antfriend/Anubis/Daughterboard/fabrication/jlcpcb_2026-07-11_r15/reports/Daughterboard_erc_report.txt

ERC report (2026-07-11T15:29:56, Encoding UTF8)
Report includes: Errors, Warnings

***** Sheet /
[footprint_link_issues]: The current configuration does not include the footprint library 'Connector_USB'
    ; warning
    @(36.83 mm, 50.80 mm): Symbol J1 [USB_C_SINK_GCT_6PAD]
[footprint_link_issues]: The current configuration does not include the footprint library 'Resistor_SMD'
    ; warning
    @(36.83 mm, 83.82 mm): Symbol R1 [TWO_PIN]
[footprint_link_issues]: The current configuration does not include the footprint library 'Resistor_SMD'
    ; warning
    @(36.83 mm, 97.79 mm): Symbol R2 [TWO_PIN]
[footprint_link_issues]: The current configuration does not include the footprint library 'Fuse'
    ; warning
    @(85.09 mm, 50.80 mm): Symbol F1 [TWO_PIN]
[footprint_link_issues]: The current configuration does not include the footprint library 'Diode_SMD'
    ; warning
    @(85.09 mm, 67.31 mm): Symbol D1 [TWO_PIN]
[footprint_link_issues]: The current configuration does not include the footprint library 'Capacitor_SMD'
    ; warning
    @(85.09 mm, 83.82 mm): Symbol C1 [TWO_PIN]
[footprint_link_issues]: The current configuration does not include the footprint library 'Capacitor_SMD'
    ; warning
    @(85.09 mm, 97.79 mm): Symbol C2 [TWO_PIN]
[footprint_link_issues]: The current configuration does not include the footprint library 'Package_TO_SOT_SMD'
    ; warning
    @(91.44 mm, 264.16 mm): Symbol U3 [AP63200WU]
[footprint_link_issues]: The current configuration does not include the footprint library 'Package_TO_SOT_SMD'
    ; warning
    @(91.44 mm, 341.63 mm): Symbol U4 [AP63200WU]
[footprint_link_issues]: The current configuration does not include the footprint library 'Fuse'
    ; warning
    @(97.79 mm, 149.86 mm): Symbol F2 [TWO_PIN]
[footprint_link_issues]: The current configuration does not include the footprint library 'Fuse'
    ; warning
    @(97.79 mm, 180.34 mm): Symbol F3 [TWO_PIN]
[footprint_link_issues]: The current configuration does not include the footprint library 'Connector_JST'
    ; warning
    @(149.86 mm, 163.83 mm): Symbol J7 [CONN_3]
[footprint_link_issues]: The current configuration does not include the footprint library 'Inductor_SMD'
    ; warning
    @(149.86 mm, 246.38 mm): Symbol L1 [TWO_PIN]
[footprint_link_issues]: The current configuration does not include the footprint library 'Capacitor_SMD'
    ; warning
    @(149.86 mm, 260.35 mm): Symbol C11 [TWO_PIN]
[footprint_link_issues]: The current configuration does not include the footprint library 'Capacitor_SMD'
    ; warning
    @(149.86 mm, 274.32 mm): Symbol C12 [TWO_PIN]
[footprint_link_issues]: The current configuration does not include the footprint library 'Resistor_SMD'
    ; warning
    @(149.86 mm, 289.56 mm): Symbol R10 [TWO_PIN]
[footprint_link_issues]: The current configuration does not include the footprint library 'Inductor_SMD'
    ; warning
    @(149.86 mm, 323.85 mm): Symbol L2 [TWO_PIN]
[footprint_link_issues]: The current configuration does not include the footprint library 'Capacitor_SMD'
    ; warning
    @(149.86 mm, 337.82 mm): Symbol C16 [TWO_PIN]
[footprint_link_issues]: The current configuration does not include the footprint library 'Capacitor_SMD'
    ; warning
    @(149.86 mm, 353.06 mm): Symbol C21 [TWO_PIN]
[footprint_link_issues]: The current configuration does not include the footprint library 'Resistor_SMD'
    ; warning
    @(149.86 mm, 367.03 mm): Symbol R13 [TWO_PIN]
[footprint_link_issues]: The current configuration does not include the footprint library 'Package_DFN_QFN'
    ; warning
    @(158.75 mm, 72.39 mm): Symbol U1 [BQ25887RGE]
[footprint_link_issues]: The current configuration does not include the footprint library 'Capacitor_SMD'
    ; warning
    @(201.93 mm, 246.38 mm): Symbol C13 [TWO_PIN]
[footprint_link_issues]: The current configuration does not include the footprint library 'Capacitor_SMD'
    ; warning
    @(201.93 mm, 260.35 mm): Symbol C14 [TWO_PIN]
[footprint_link_issues]: The current configuration does not include the footprint library 'Capacitor_SMD'
    ; warning
    @(201.93 mm, 274.32 mm): Symbol C15 [TWO_PIN]
[footprint_link_issues]: The current configuration does not include the footprint library 'Resistor_SMD'
    ; warning
    @(201.93 mm, 289.56 mm): Symbol R8 [TWO_PIN]
[footprint_link_issues]: The current configuration does not include the footprint library 'Resistor_SMD'
    ; warning
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

 ** ERC messages: 157  Errors 0  Warnings 157

 ** Ignored checks:
    - Global label only appears once in the schematic
    - Four connection points are joined together
    - SPICE model issue
    - Assigned footprint doesn't match footprint filters
