antfriend/Anubis/Daughterboard/fetoptions.bmp

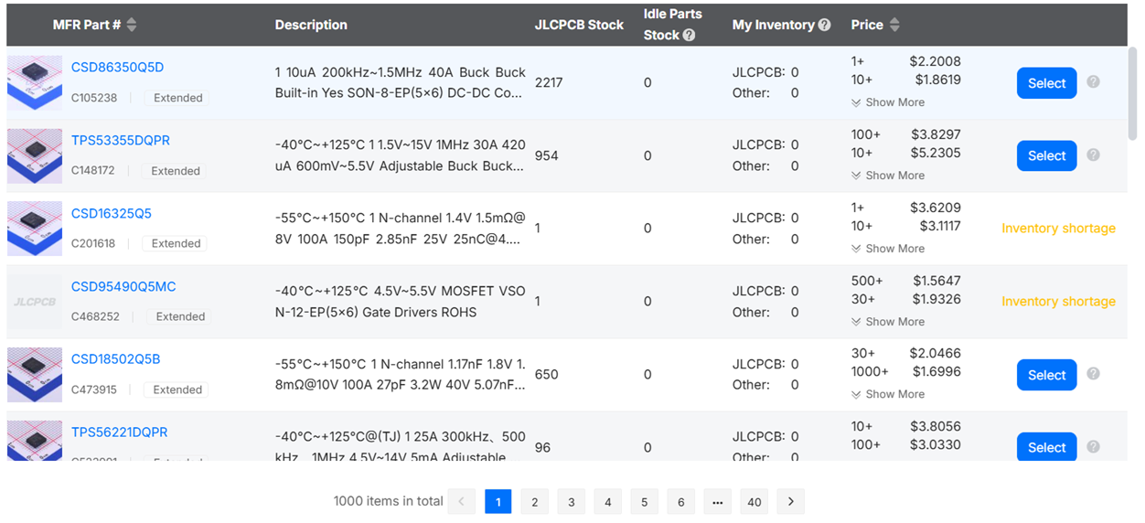
Daughterboard/fetoptions.bmp
