antfriend/Anubis/Daughterboard/tmp_csd18502_page8_vectors.png

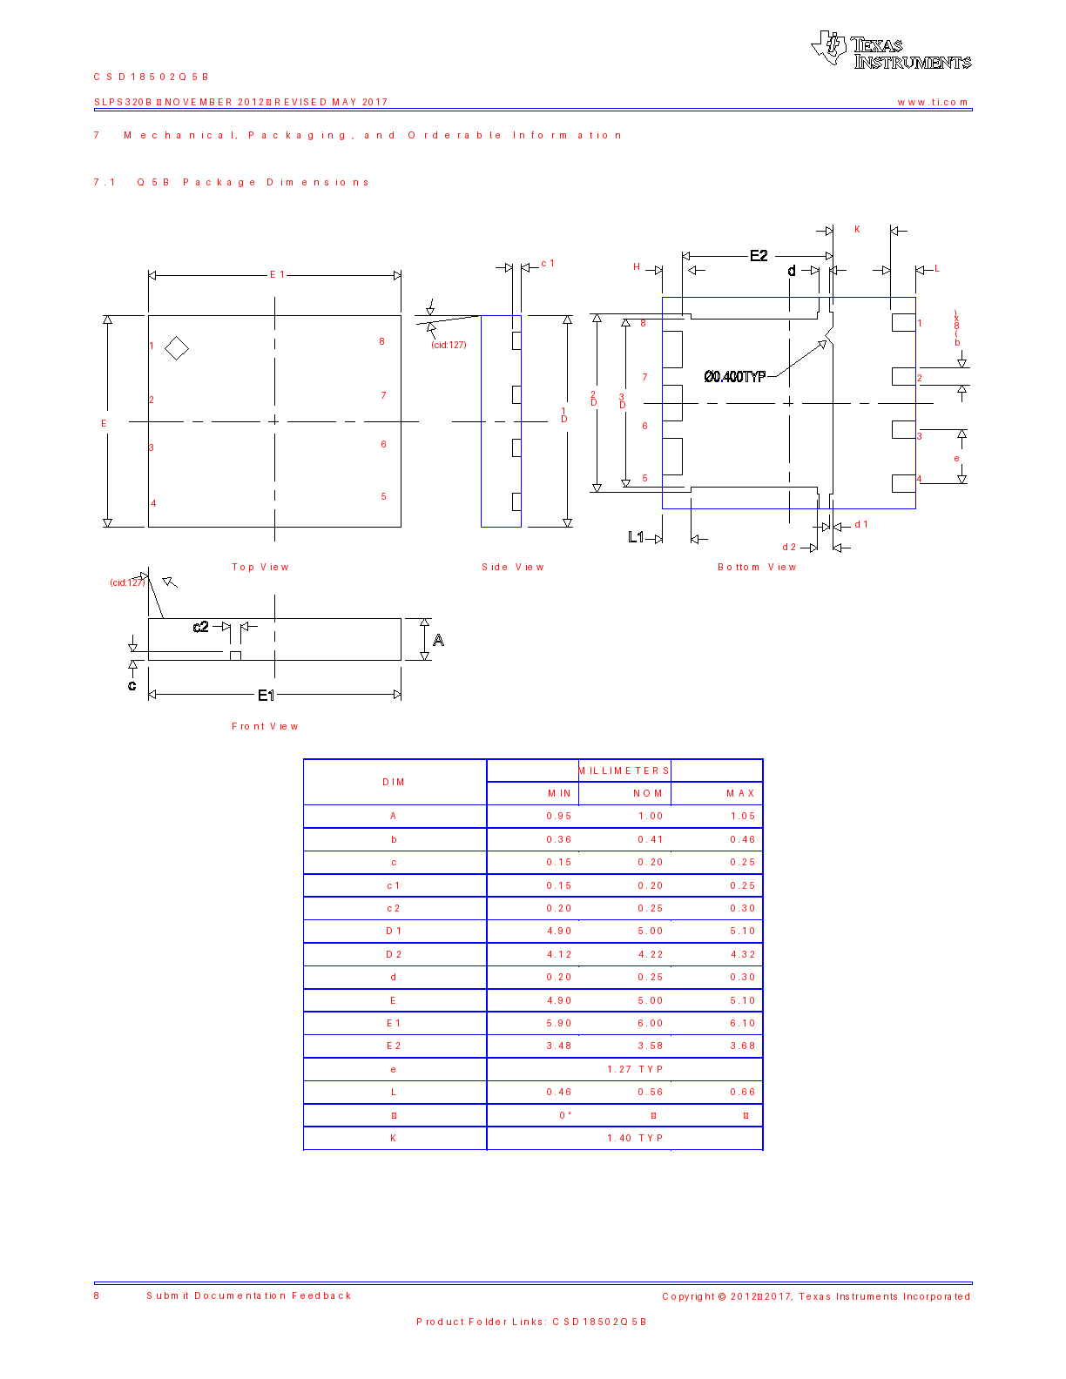
Daughterboard/tmp_csd18502_page8_vectors.png
