antfriend/Anubis/Daughterboard/tmp_csd18502_page9_vectors.png

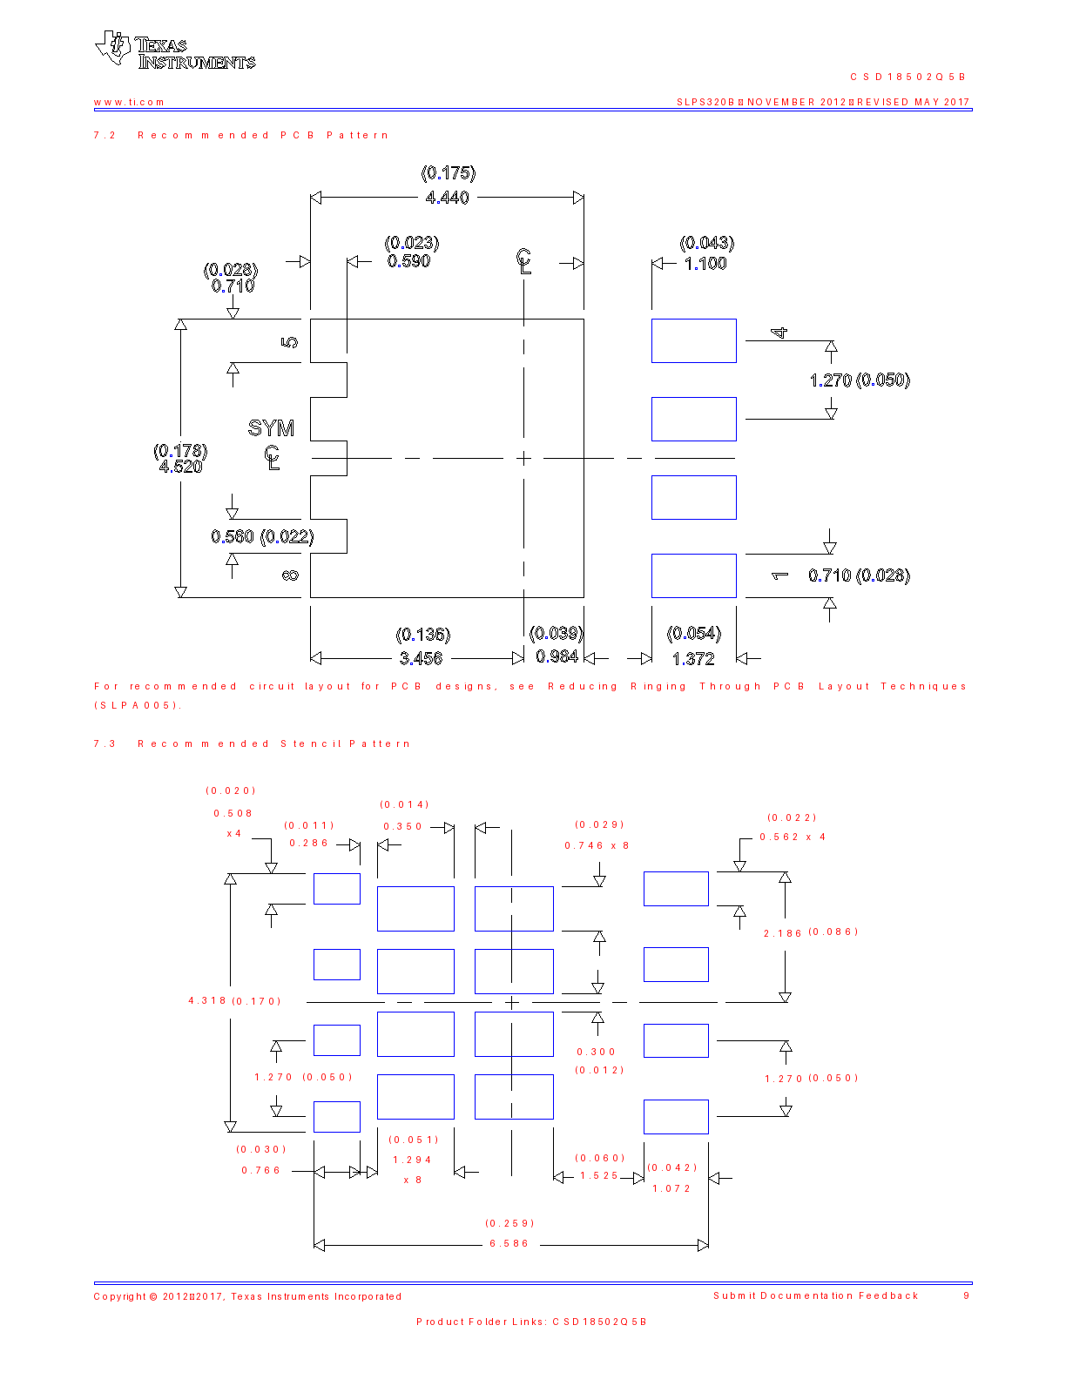
Daughterboard/tmp_csd18502_page9_vectors.png
