antfriend/Anubis/Daughterboard/x5Bottom.webp

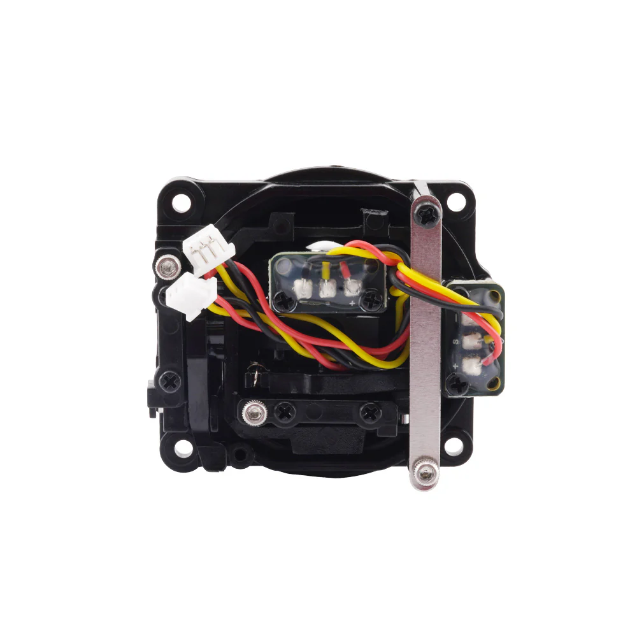
Daughterboard/x5Bottom.webp
