antfriend/Anubis/Daughterboard/x5Front.webp

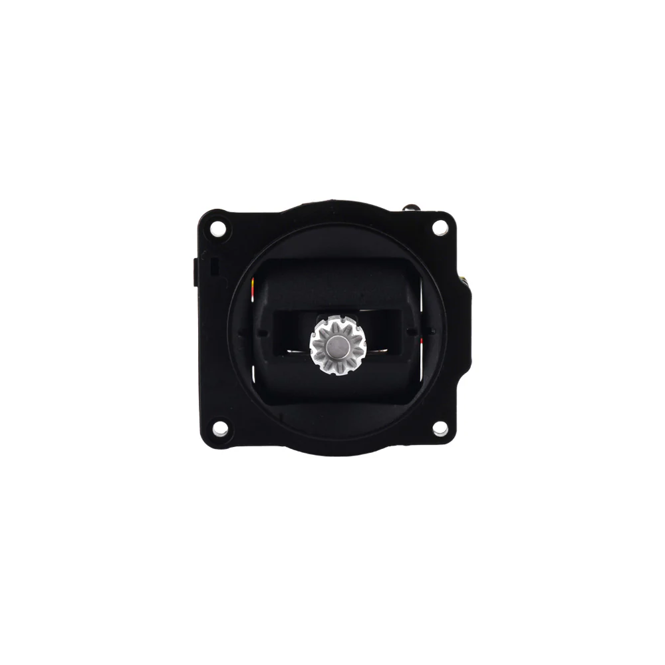
Daughterboard/x5Front.webp
