antfriend/Anubis/Hosyond_apr24b/Daughterboard/Daughterboard_pcb_bcu_ground_zone_preview.png

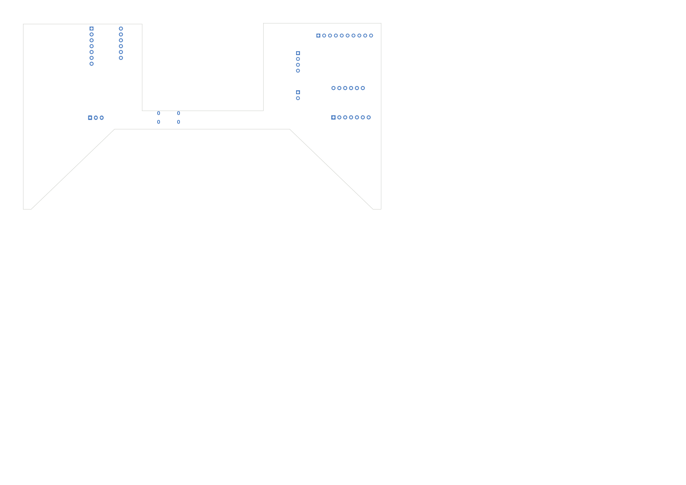
Hosyond_apr24b/Daughterboard/Daughterboard_pcb_bcu_ground_zone_preview.png
