antfriend/Anubis/Hosyond_apr24b/Daughterboard/Daughterboard_pcb_j30_5v_pad_preview.png

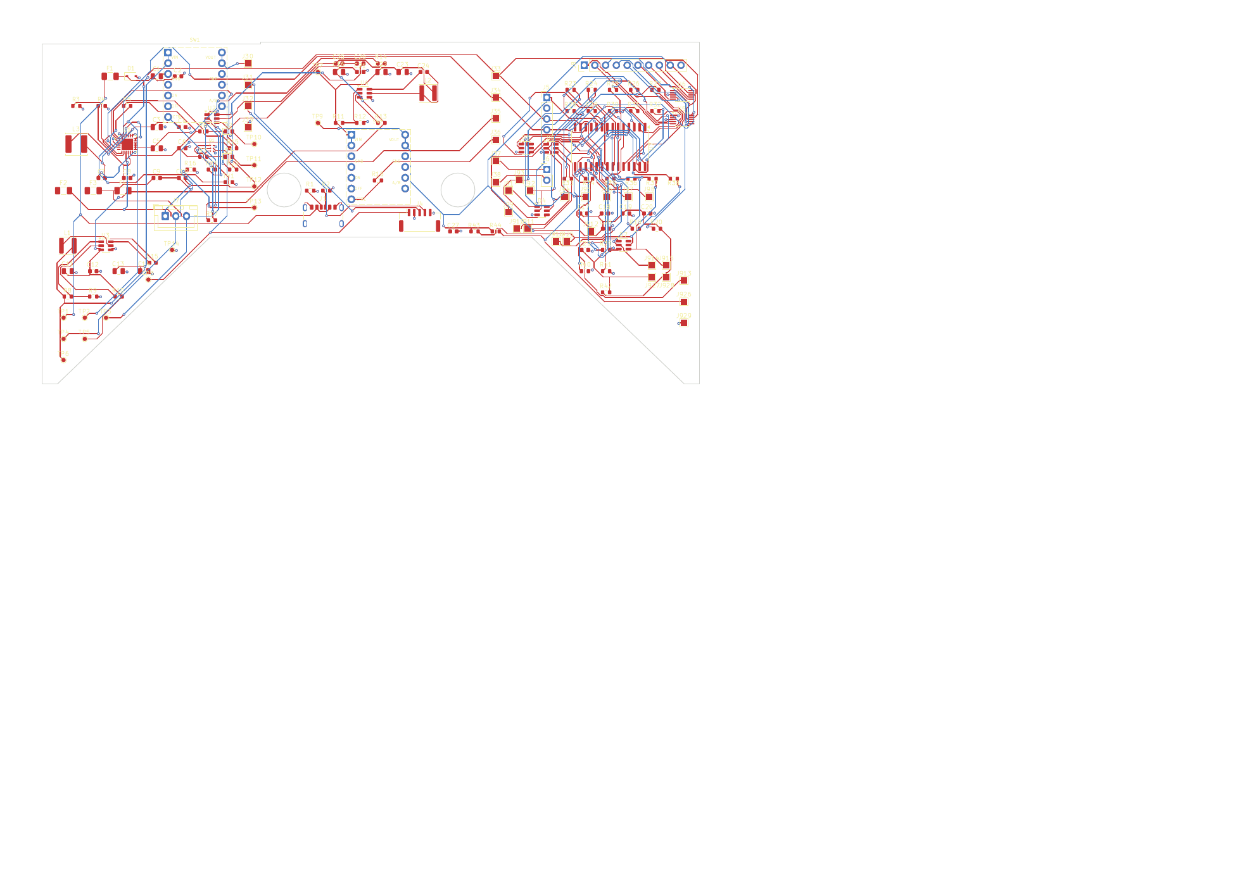
Hosyond_apr24b/Daughterboard/Daughterboard_pcb_j30_5v_pad_preview.png
