antfriend/Anubis/Hosyond_apr24b/Daughterboard/Daughterboard_pcb_power_widened_preview.png

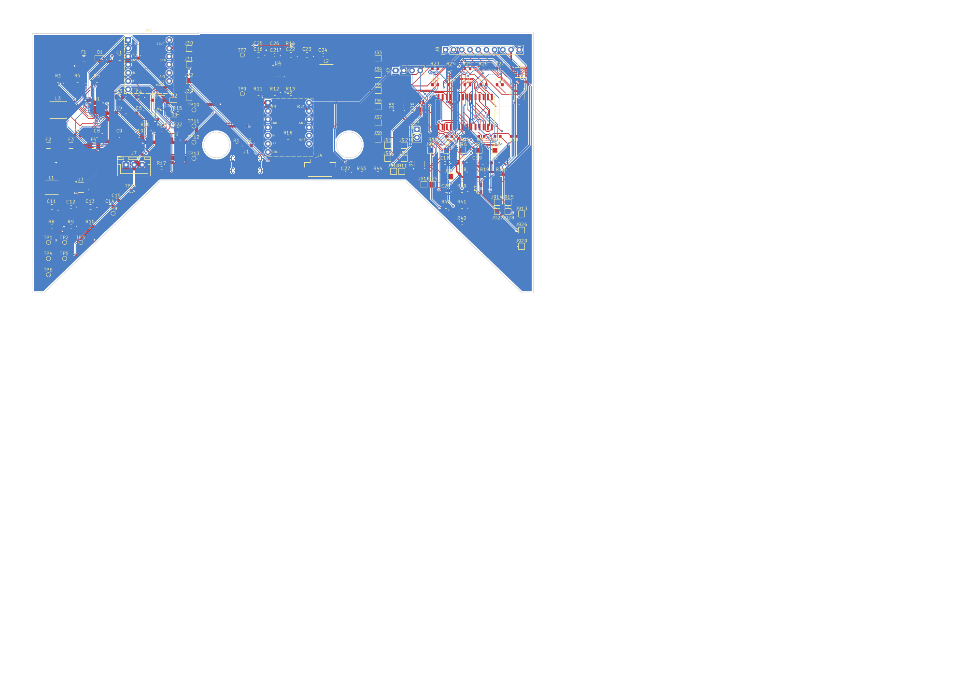
Hosyond_apr24b/Daughterboard/Daughterboard_pcb_power_widened_preview.png
