antfriend/Anubis/Hosyond_apr24b/Daughterboard/Daughterboard_pinlevel_preview-1.png

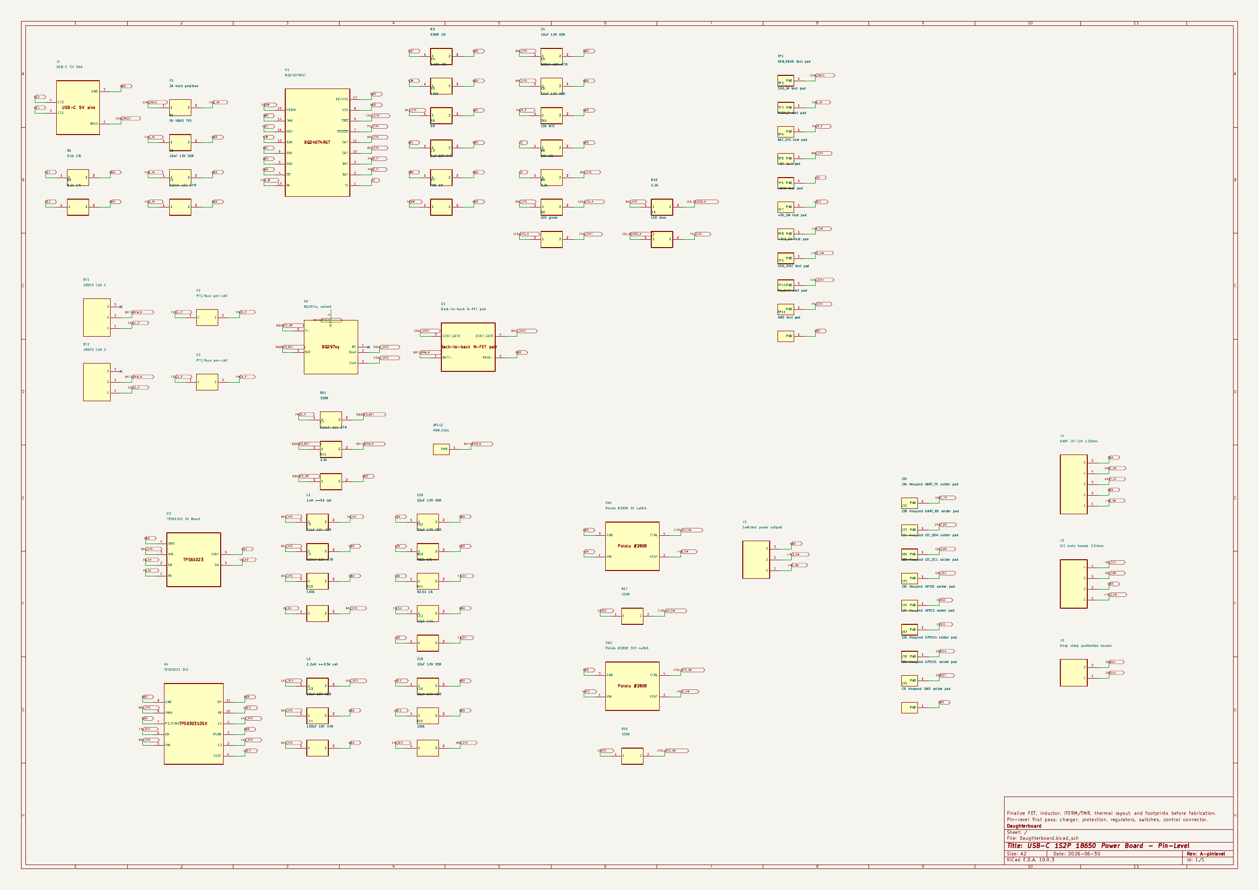
Hosyond_apr24b/Daughterboard/Daughterboard_pinlevel_preview-1.png
