antfriend/Anubis/Hosyond_apr24b/Daughterboard/Daughterboard_pinlevel.pdf

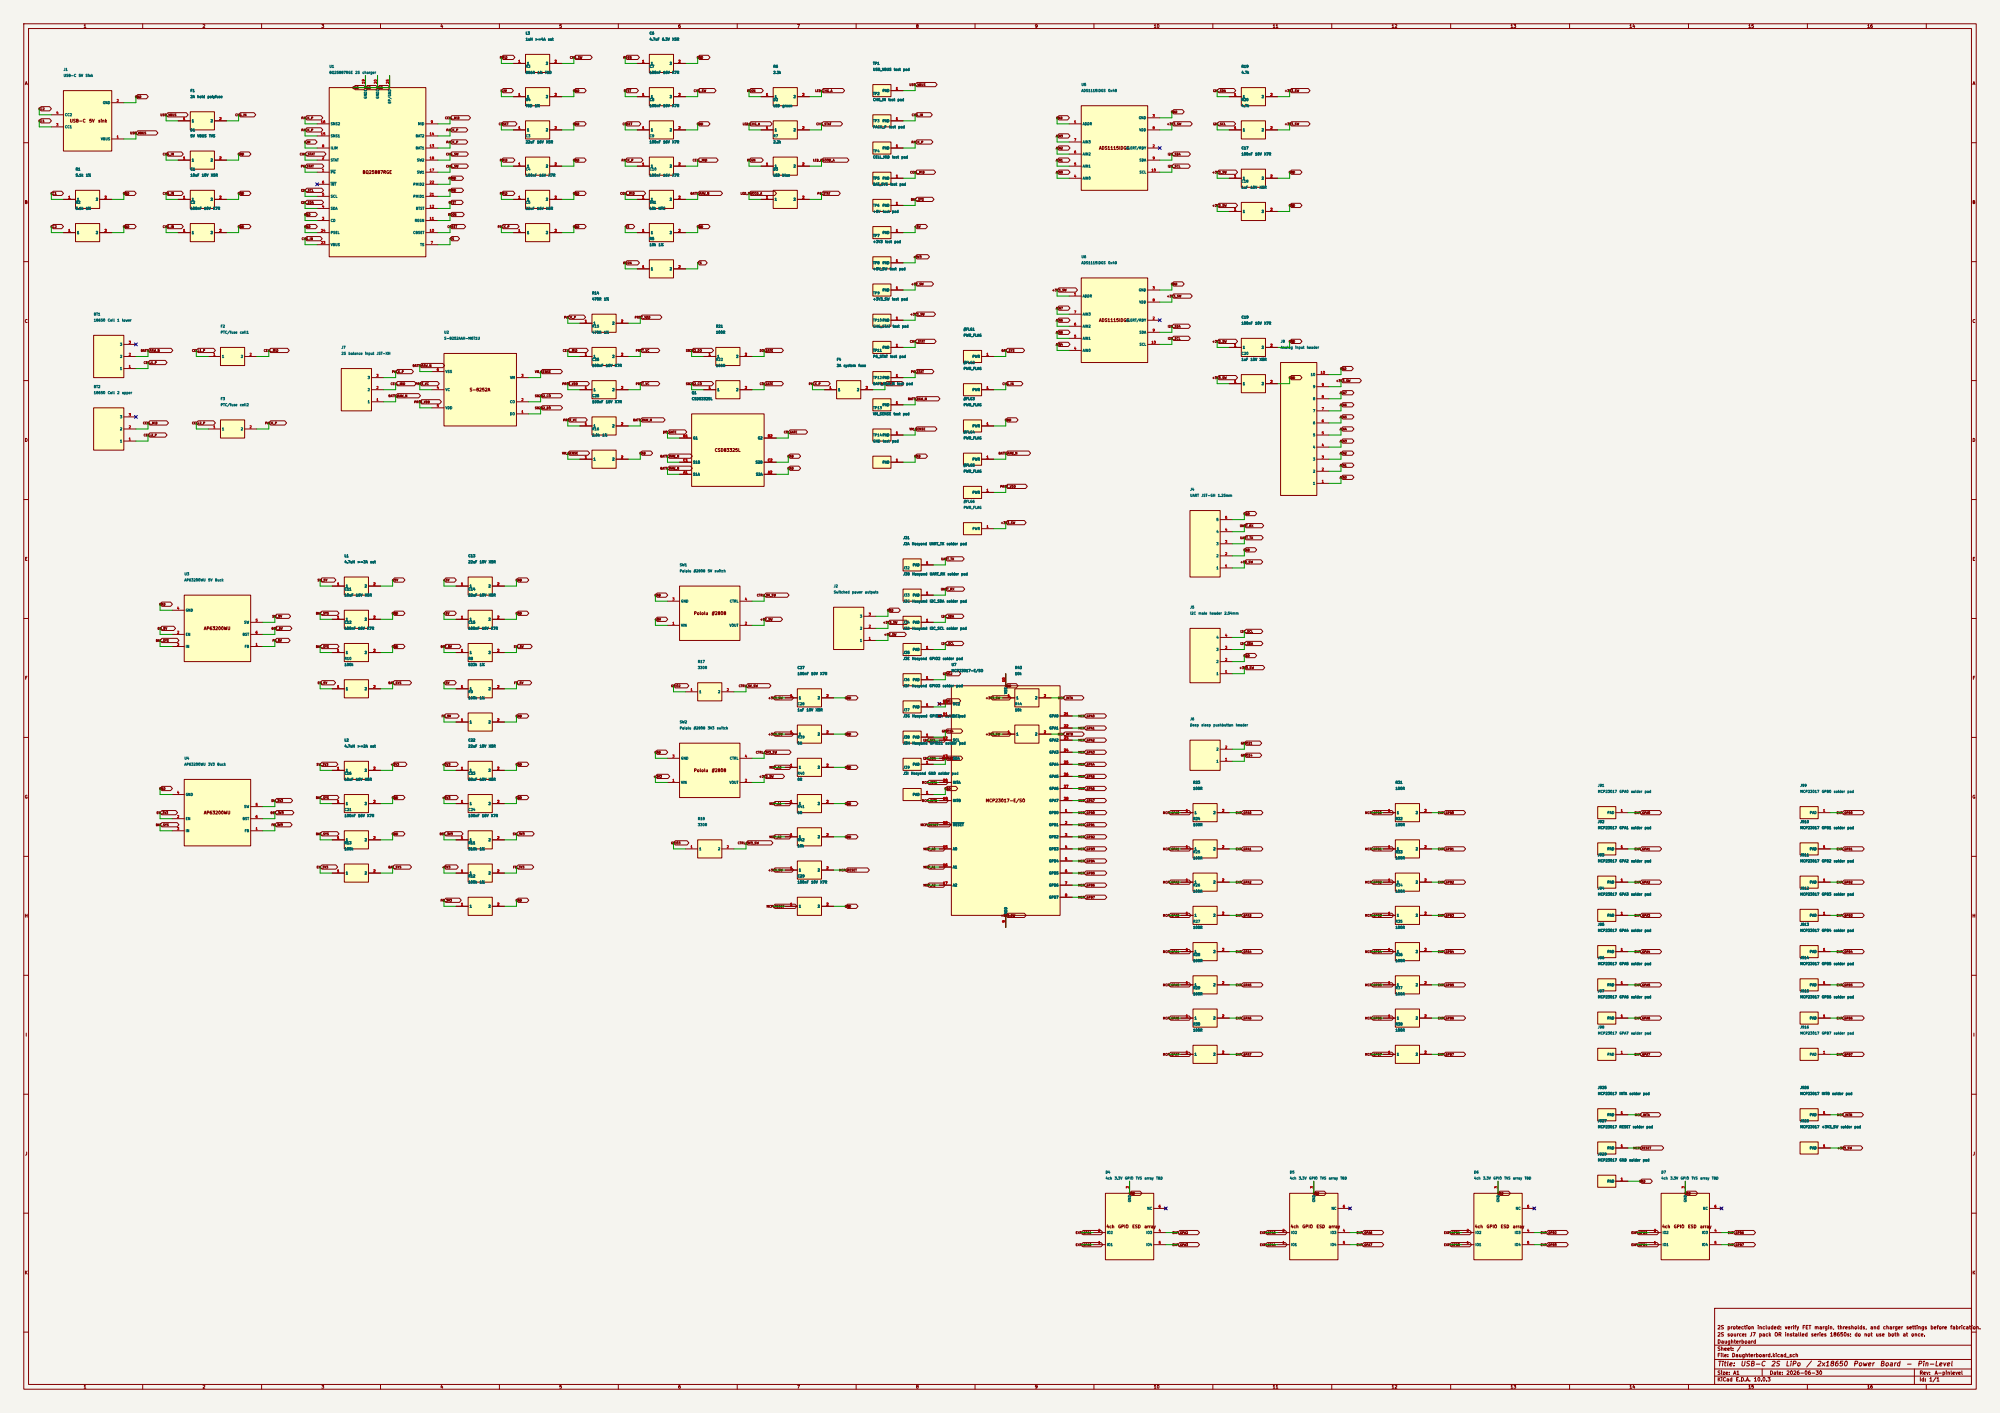
[picture p25: page 1]

2S balance input JST-XH

TP14 GND test pad PAD
PAD

J3A Hosyond UART_TX solder pad PAD

J3B Hosyond UART_RX solder pad PAD

J3C Hosyond I2C_SDA solder pad PAD

J3D Hosyond I2C_SCL solder pad PAD

J3E Hosyond GPIO2 solder pad PAD

J3F Hosyond GPIO3 solder pad PAD

J3G Hosyond GPIO14 solder pad PAD

J3H Hosyond GPIO21 solder pad PAD

J926 MCP23017 INTB solder pad 4ch GPIO ESD array

J925 MCP23017 INTA solder pad PAD

J926 MCP23017 INTB solder pad PAD

J929 MCP23017 GND solder pad PAD

J927 MCP23017 RESET solder pad PAD

4ch 3.3V GPIO TVS array TBD

2S source: J7 pack OR installed series 18650s; do not use both at once. 2S protection included; verify FET margin, thresholds, and charger settings before fabrication.

Daughterboard
Sheet: /
File: Daughterboard.kicad_sch
Title: USB-C 2S LiPo / 2x18650 Power Board - Pin-Level

Size: A1 | Rev: A-pinlevel
KiCad E.D.A. 10.0.3 | Id: 1/1
