antfriend/Anubis/Hosyond_apr24b/Daughterboard/Daughterboard_pcb_rebalanced_pre_route.pdf

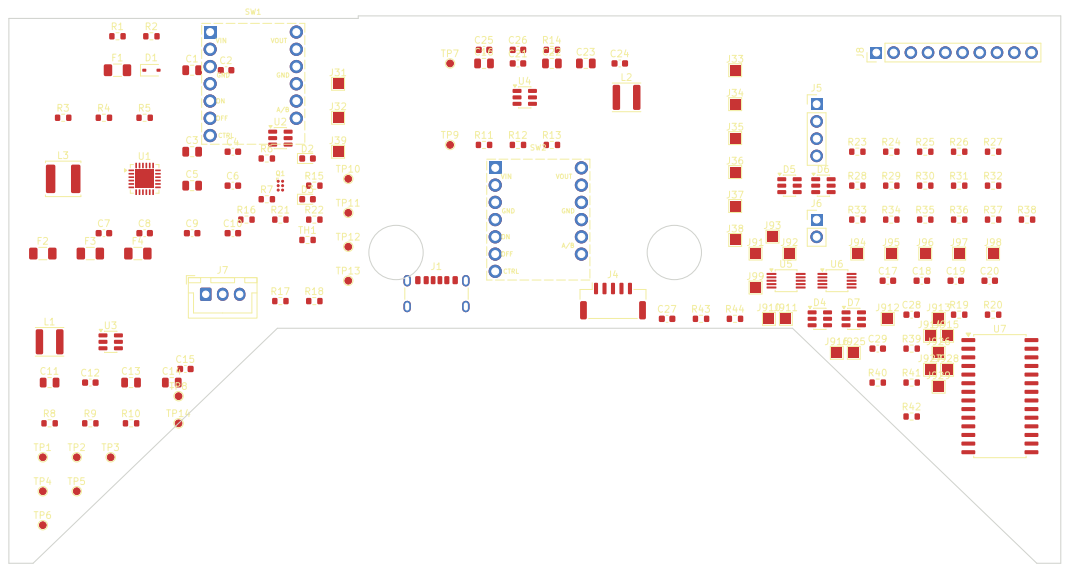
[picture p32: page 1]
