antfriend/Anubis/Hosyond_apr24b/Daughterboard/Daughterboard_pcb_review.pdf

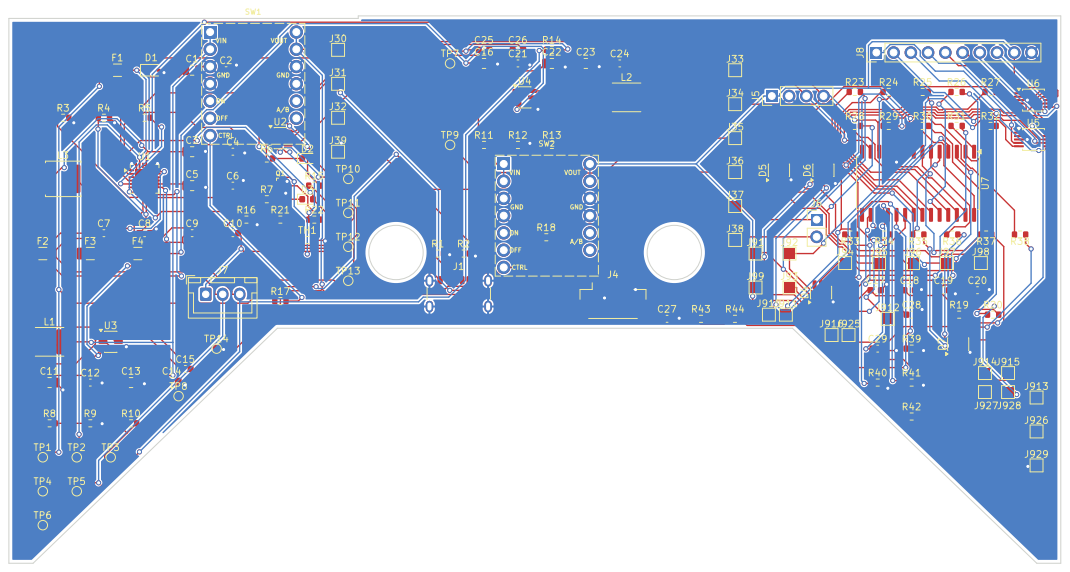
[picture p33: page 1]
