antfriend/Anubis/Hosyond_apr24b/Daughterboard/Daughterboard_pcb_unrouted.pdf

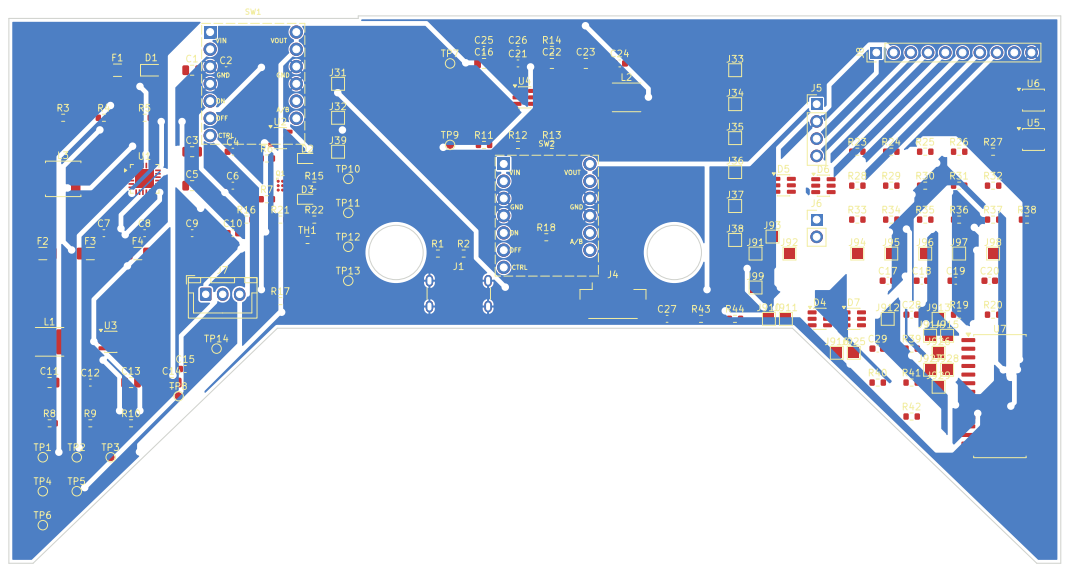
[picture p34: page 1]
