antfriend/Anubis/Hosyond_apr24b/Daughterboard/Daughterboard_pcb_usb_cc_moved.pdf

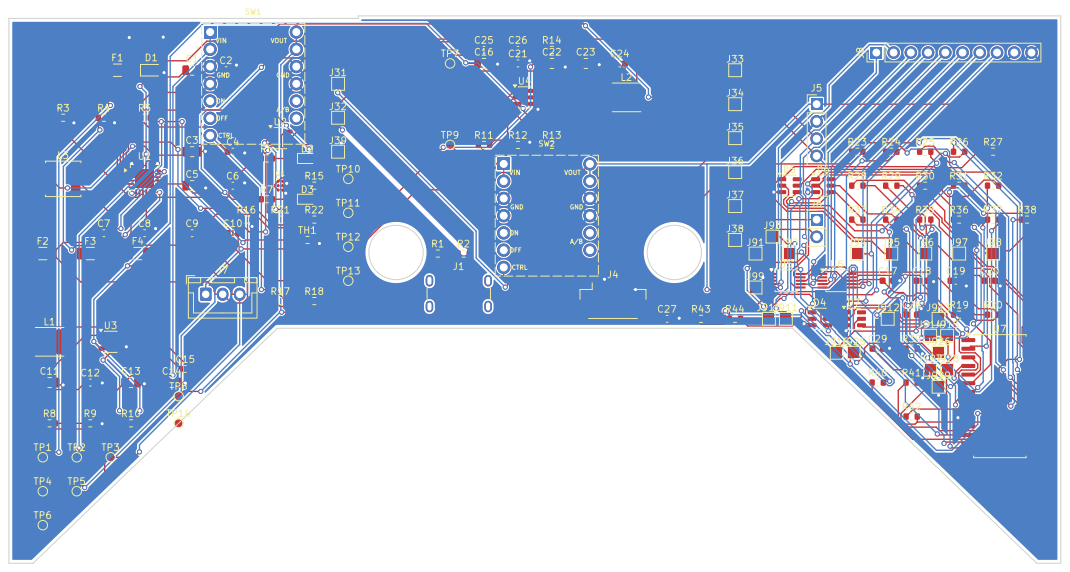
[picture p35: page 1]
